overset/JP01/V1.1/images/b2-sm.jpeg

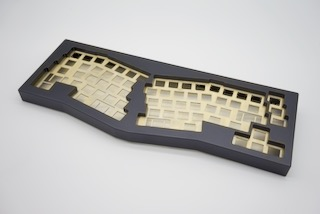
V1.1/images/b2-sm.jpeg
