overset/JP01/V1.1/images/parts_switch_plates.jpeg

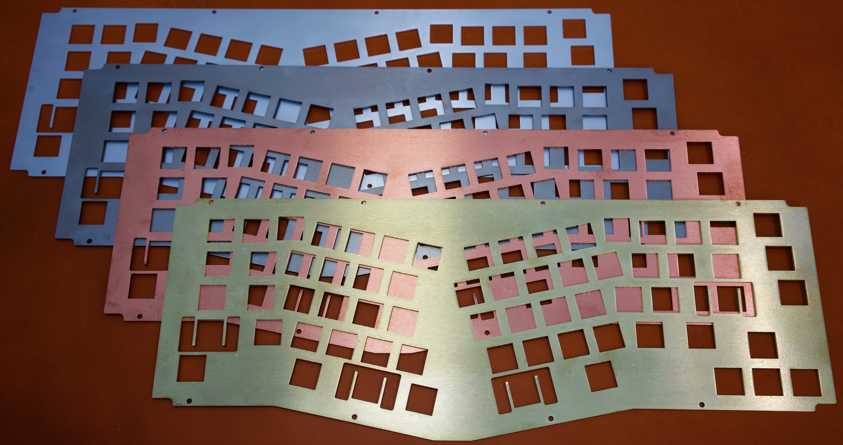
V1.1/images/parts_switch_plates.jpeg
