overset/JP01/V1.1/base-plate_laser-cut.dxf

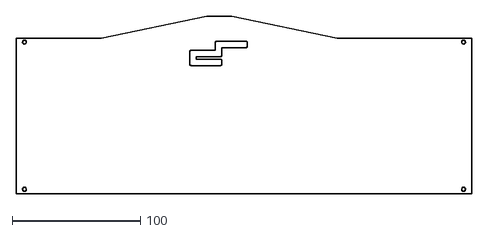
[picture p42: CAD file, 2020-05-06]
V1.1/base-plate_laser-cut.dxf
355.6 x 138.6
