overset/JP01/V1.1/gasket_switch-plate.dxf

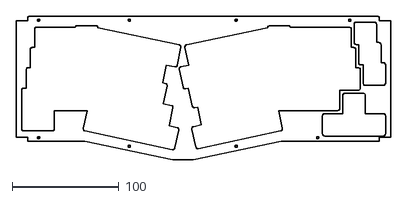
[picture p43: CAD file, 2020-05-06]
V1.1/gasket_switch-plate.dxf
351.0 x 134.0
