overset/JP01/V1.1/images/fitment_assembled_front.jpeg

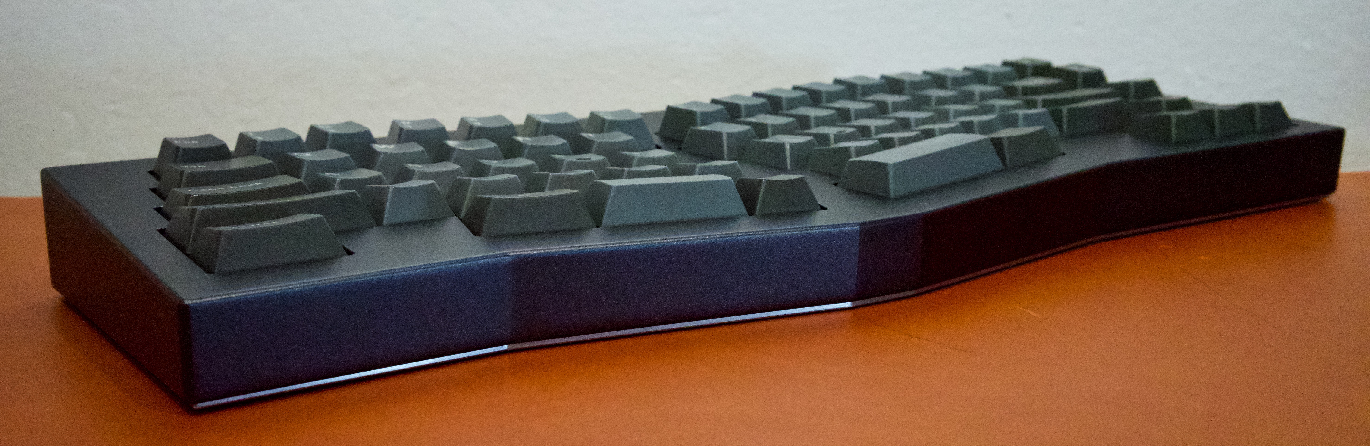
V1.1/images/fitment_assembled_front.jpeg
