overset/JP01/V1.1/images/fitment_assembled_right.jpeg

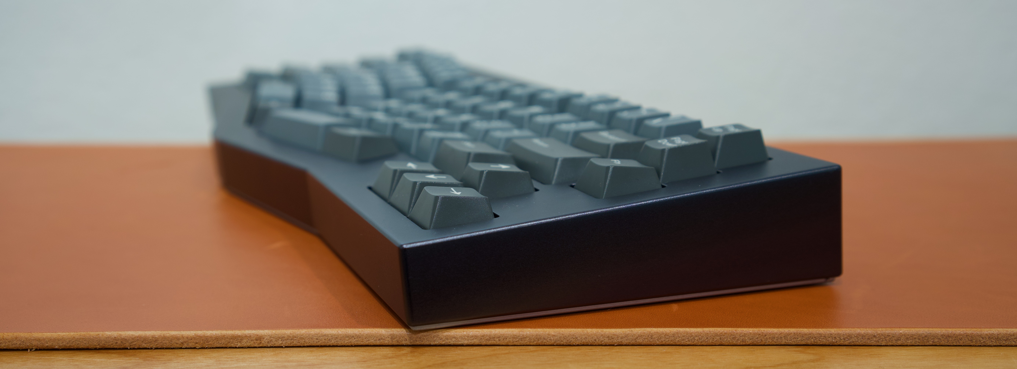
V1.1/images/fitment_assembled_right.jpeg
