overset/JP01/V1.1/images/test_assembled_aluminum.jpeg

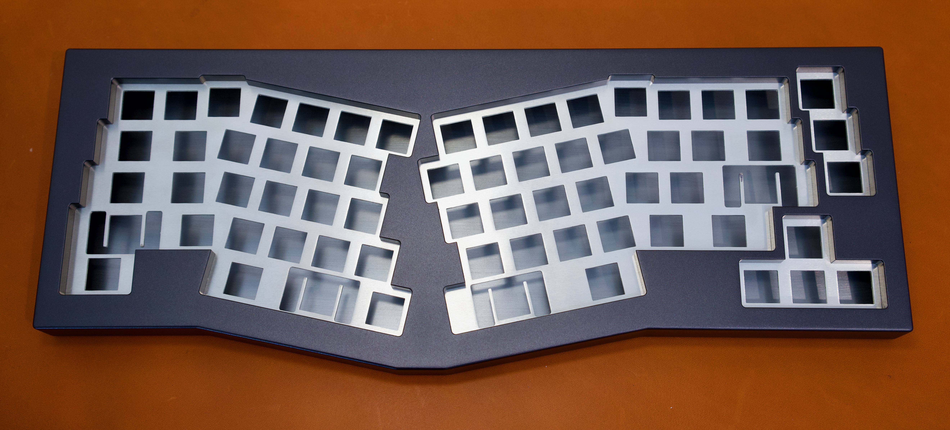
V1.1/images/test_assembled_aluminum.jpeg
