overset/JP01/V1.1/images/test_assembly_bottom.jpeg

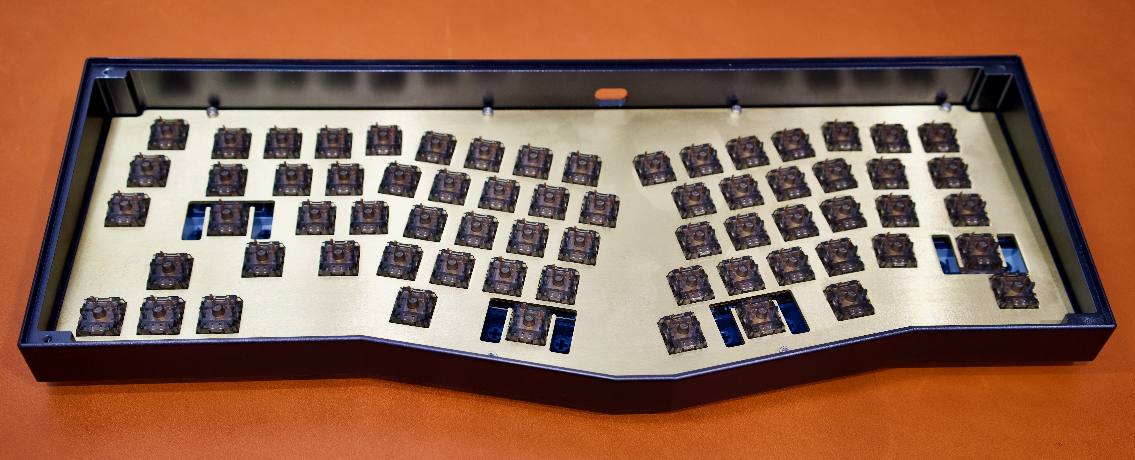
V1.1/images/test_assembly_bottom.jpeg
