overset/JP01/V1.1/images/test_assembly_pcb.jpeg

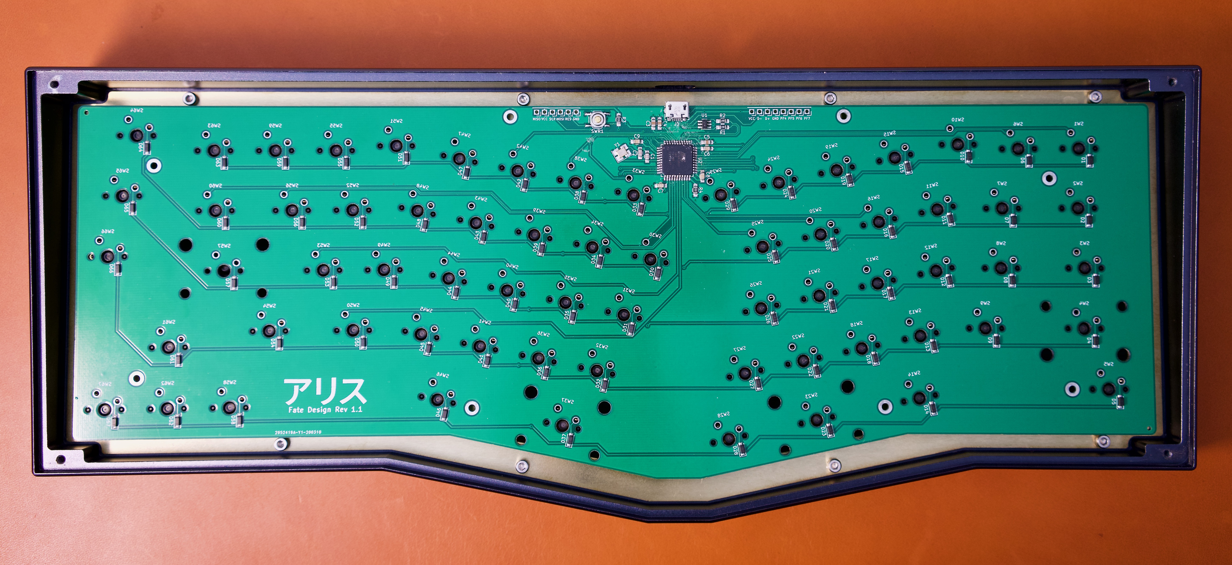
V1.1/images/test_assembly_pcb.jpeg
